matteob29/Stage_-_Robot_Differentiel_pilotable/Meca/coque avant.SLDPRT

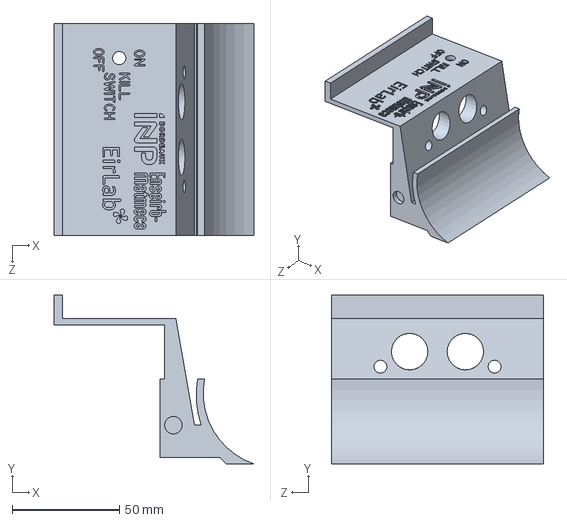
[picture p35: CAD file, 2025-10-29]
Meca/coque avant.SLDPRT
93.3 x 78.8 x 98.9 mm
