matteob29/Stage_-_Robot_Differentiel_pilotable/Meca/STL_STEP/structure.3mf

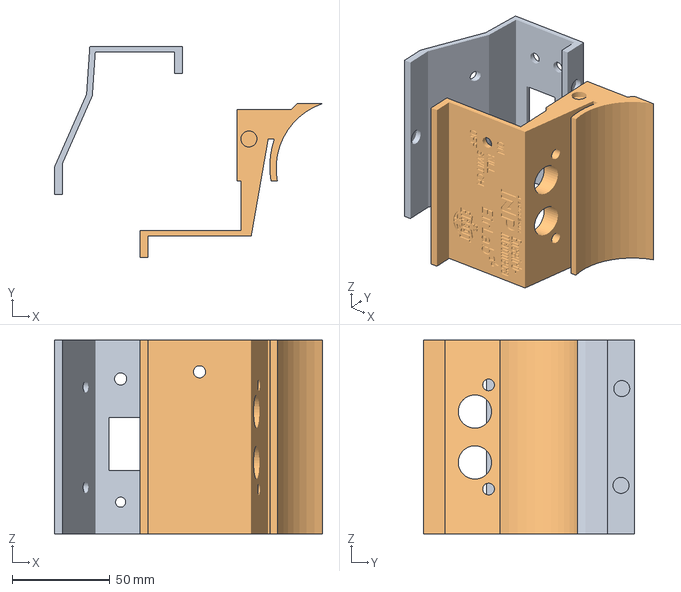
[picture p36: CAD file, 2025-10-29]
Meca/STL_STEP/structure.3mf
136.9 x 108.0 x 98.9 mm
coque arrière.STL
coque avant.STL
