matteob29/Stage_-_Robot_Differentiel_pilotable/Meca/plaque_bas.SLDPRT

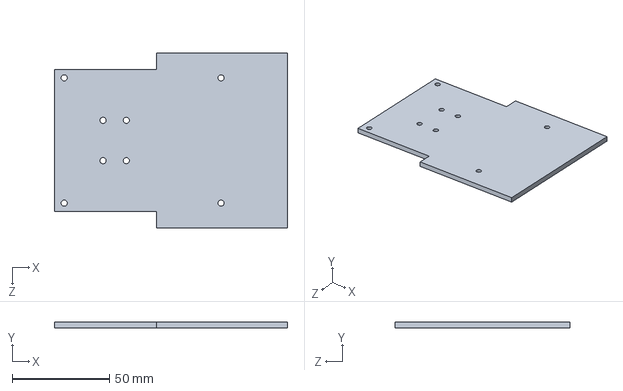
[picture p37: CAD file, 2025-10-29]
Meca/plaque_bas.SLDPRT
120.0 x 3.00 x 90.0 mm
