matteob29/Stage_-_Robot_Differentiel_pilotable/Meca/roue.SLDPRT

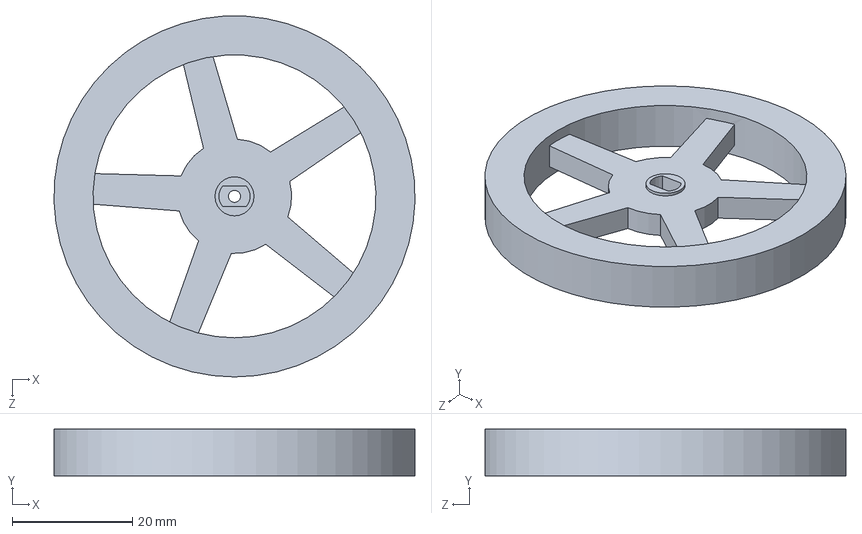
[picture p38: CAD file, 2025-10-29]
Meca/roue.SLDPRT
60.0 x 7.80 x 59.9 mm
