matteob29/Stage_-_Robot_Differentiel_pilotable/Meca/entretoise_avant.SLDPRT

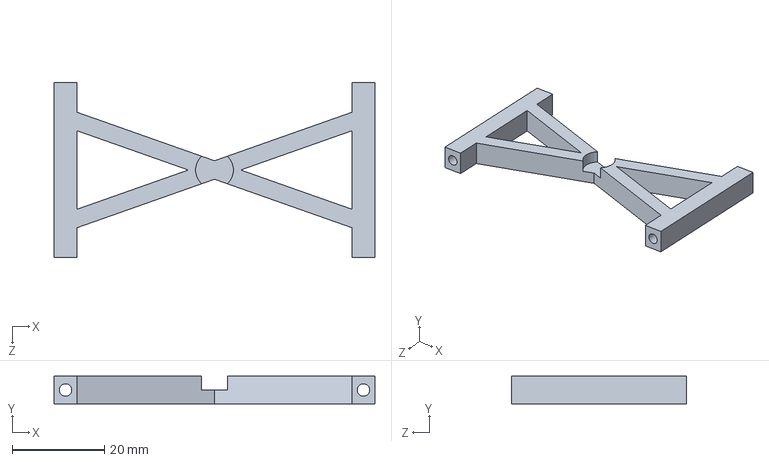
[picture p39: CAD file, 2025-10-29]
Meca/entretoise_avant.SLDPRT
69.5 x 6.00 x 38.0 mm
