matteob29/Stage_-_Robot_Differentiel_pilotable/Meca/Mirrorsupport_moteurs.SLDPRT

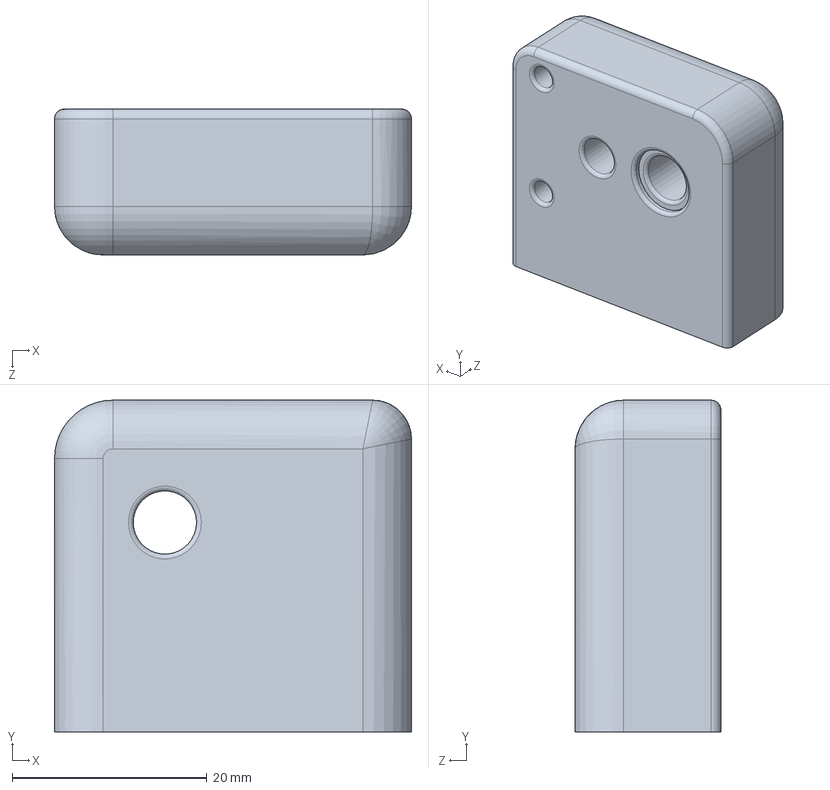
[picture p40: CAD file, 2025-10-29]
Meca/Mirrorsupport_moteurs.SLDPRT
36.7 x 34.1 x 15.0 mm
