matteob29/Stage_-_Robot_Differentiel_pilotable/Meca/stand.SLDPRT

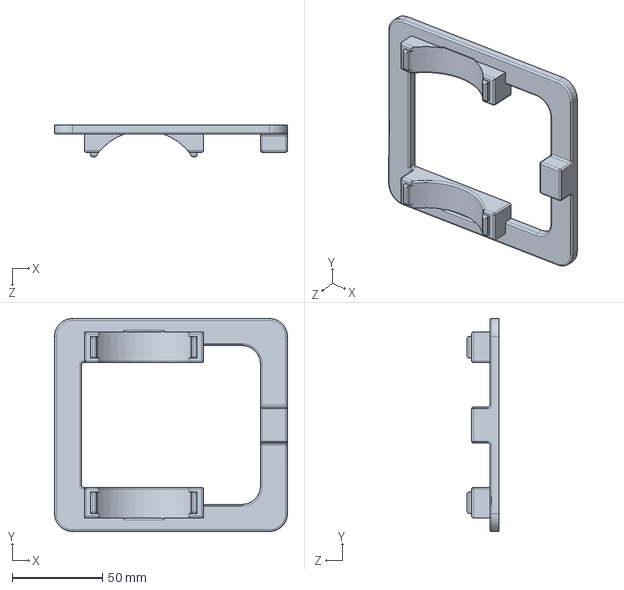
[picture p41: CAD file, 2025-10-29]
Meca/stand.SLDPRT
129.0 x 117.9 x 17.5 mm
