matteob29/Stage_-_Robot_Differentiel_pilotable/Meca/entretoise_derriere.SLDPRT

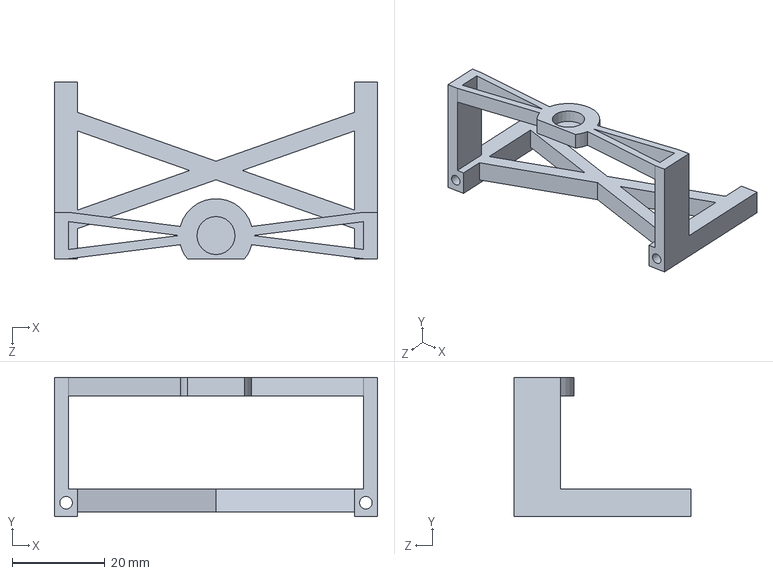
[picture p42: CAD file, 2025-10-29]
Meca/entretoise_derriere.SLDPRT
69.5 x 30.0 x 38.0 mm
