matteob29/Stage_-_Robot_Differentiel_pilotable/Meca/L298N Motor Driver.SLDPRT

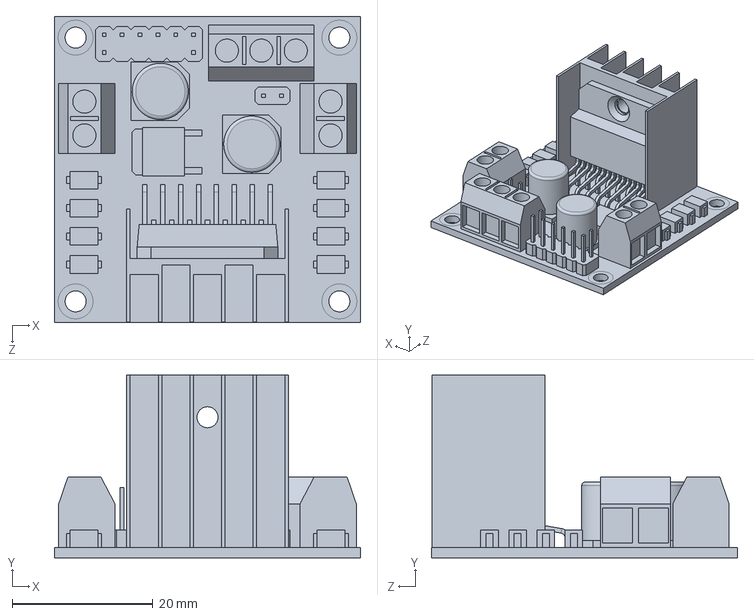
[picture p43: CAD file, 2025-10-29]
Meca/L298N Motor Driver.SLDPRT
43.5 x 26.0 x 43.5 mm
