matteob29/Stage_-_Robot_Differentiel_pilotable/Meca/coque côté.SLDPRT

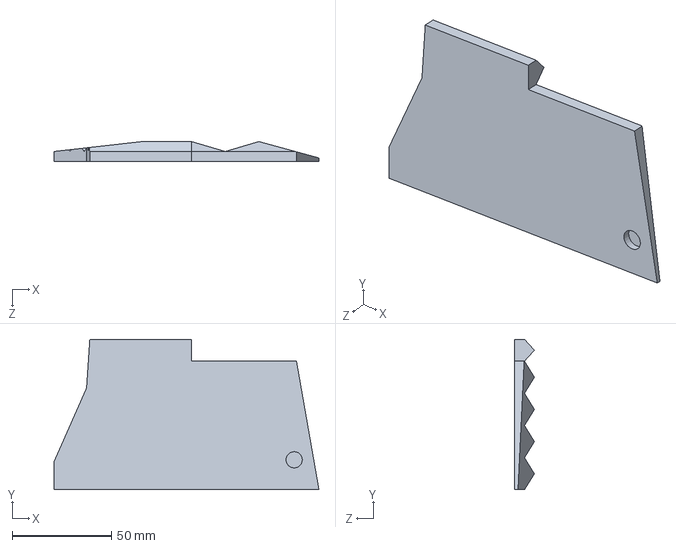
[picture p44: CAD file, 2025-10-29]
Meca/coque côté.SLDPRT
133.5 x 75.8 x 10.0 mm
